lle/defcon31-addon/img/cubeMX.png

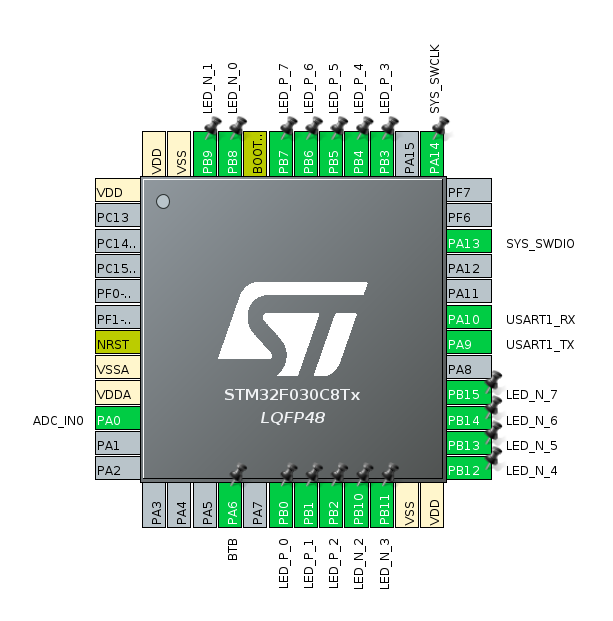
img/cubeMX.png
