lle/defcon31-addon/img/cubeMX_adc.png

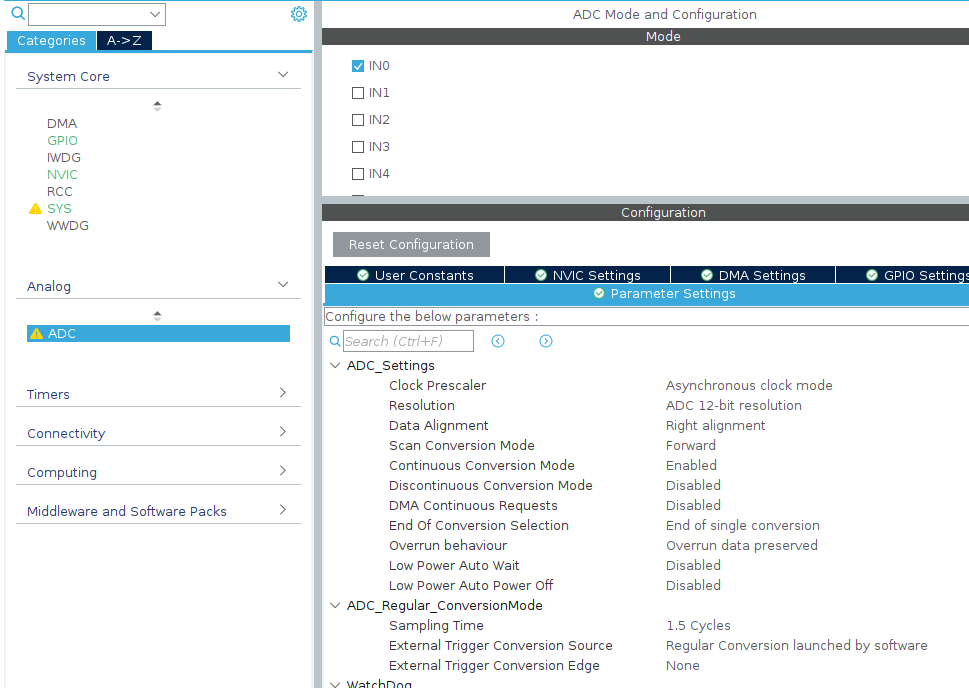
img/cubeMX_adc.png
