lle/defcon31-addon/img/cubeMX_clock.png

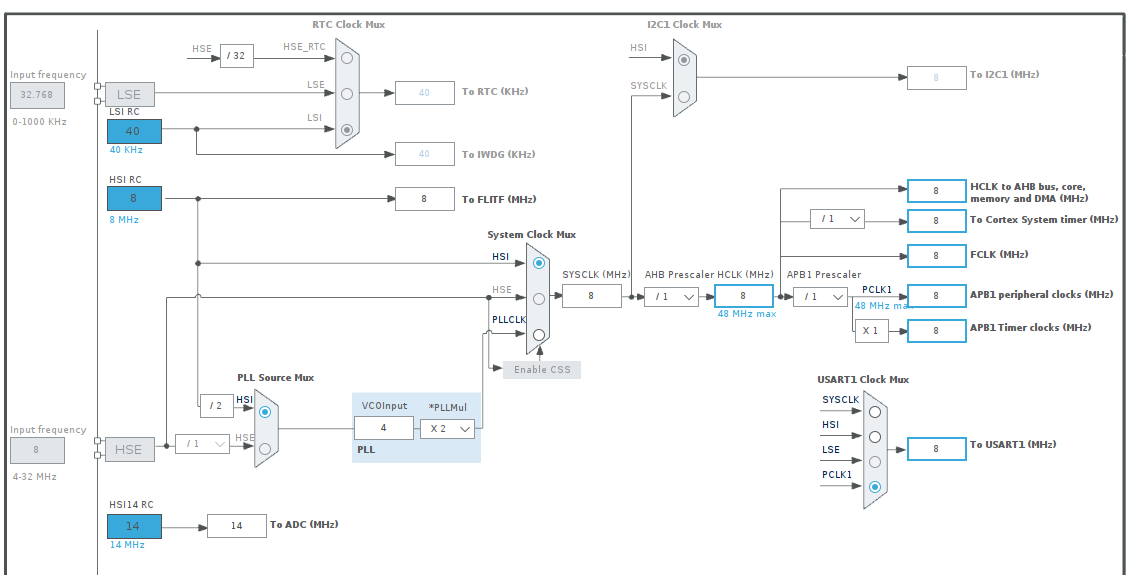
img/cubeMX_clock.png
