lle/defcon31-addon/img/cubeMX_project.png

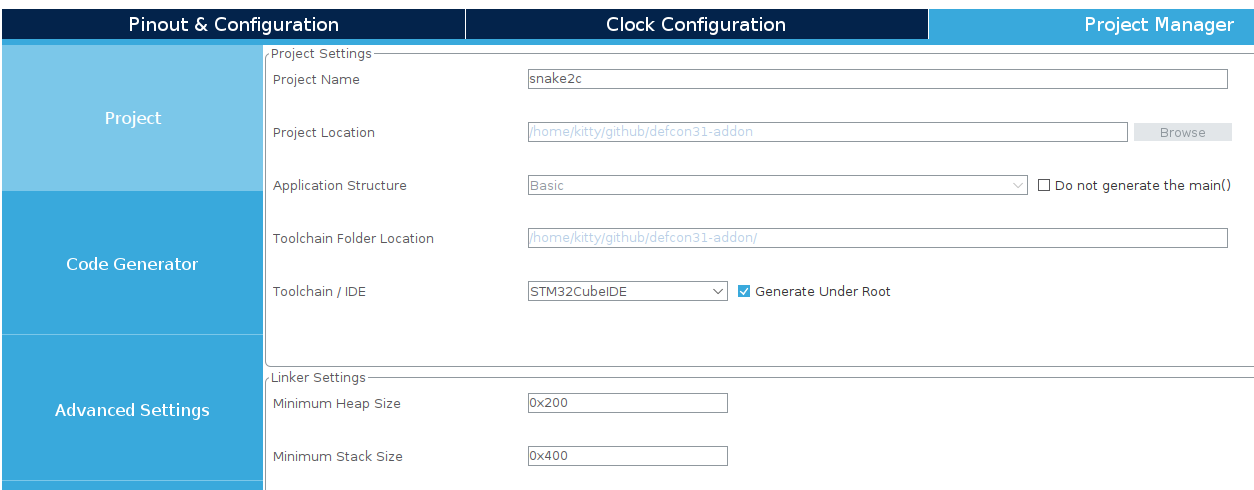
img/cubeMX_project.png
