lle/defcon31-addon/img/cubeMX_tim16nvic.png

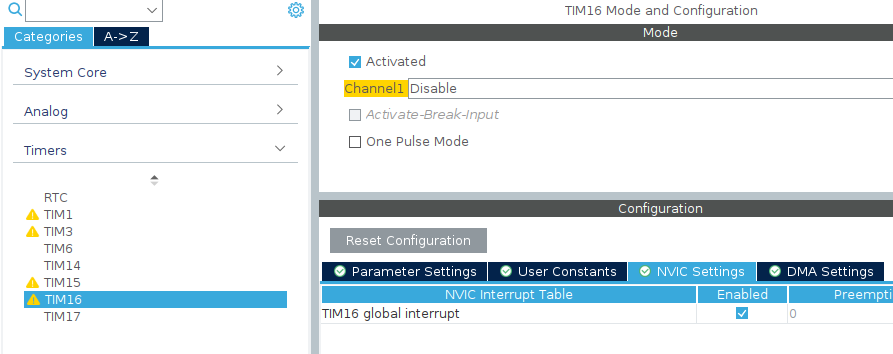
img/cubeMX_tim16nvic.png
