lle/defcon31-addon/img/cubeMX_timer16.png

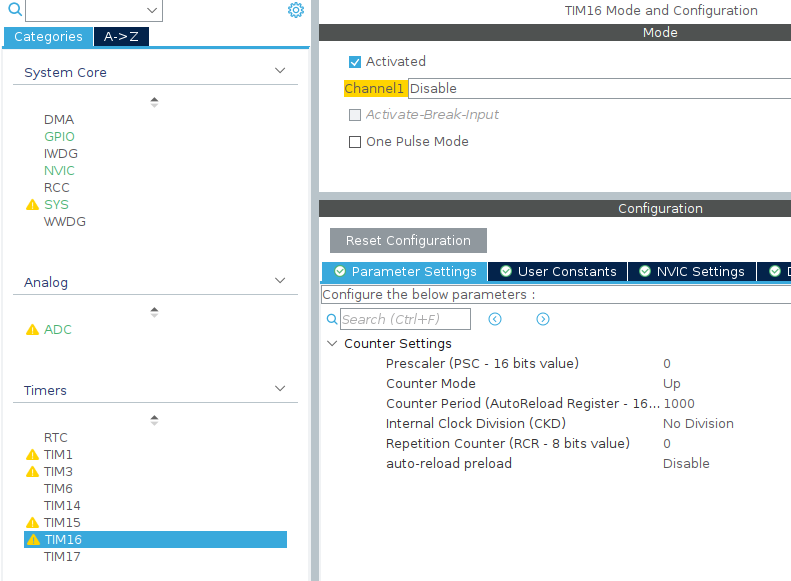
img/cubeMX_timer16.png
