lle/defcon31-addon/img/cubeMX_uart.png

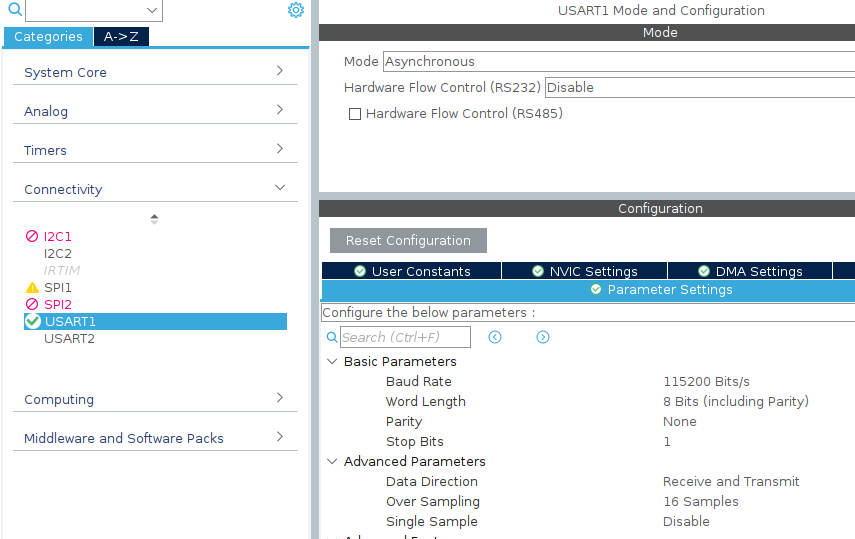
img/cubeMX_uart.png
